ahradnansky/GearIndicator/resources/_HWcomponents/DISP/Q01_ZTTCR8MG.pdf

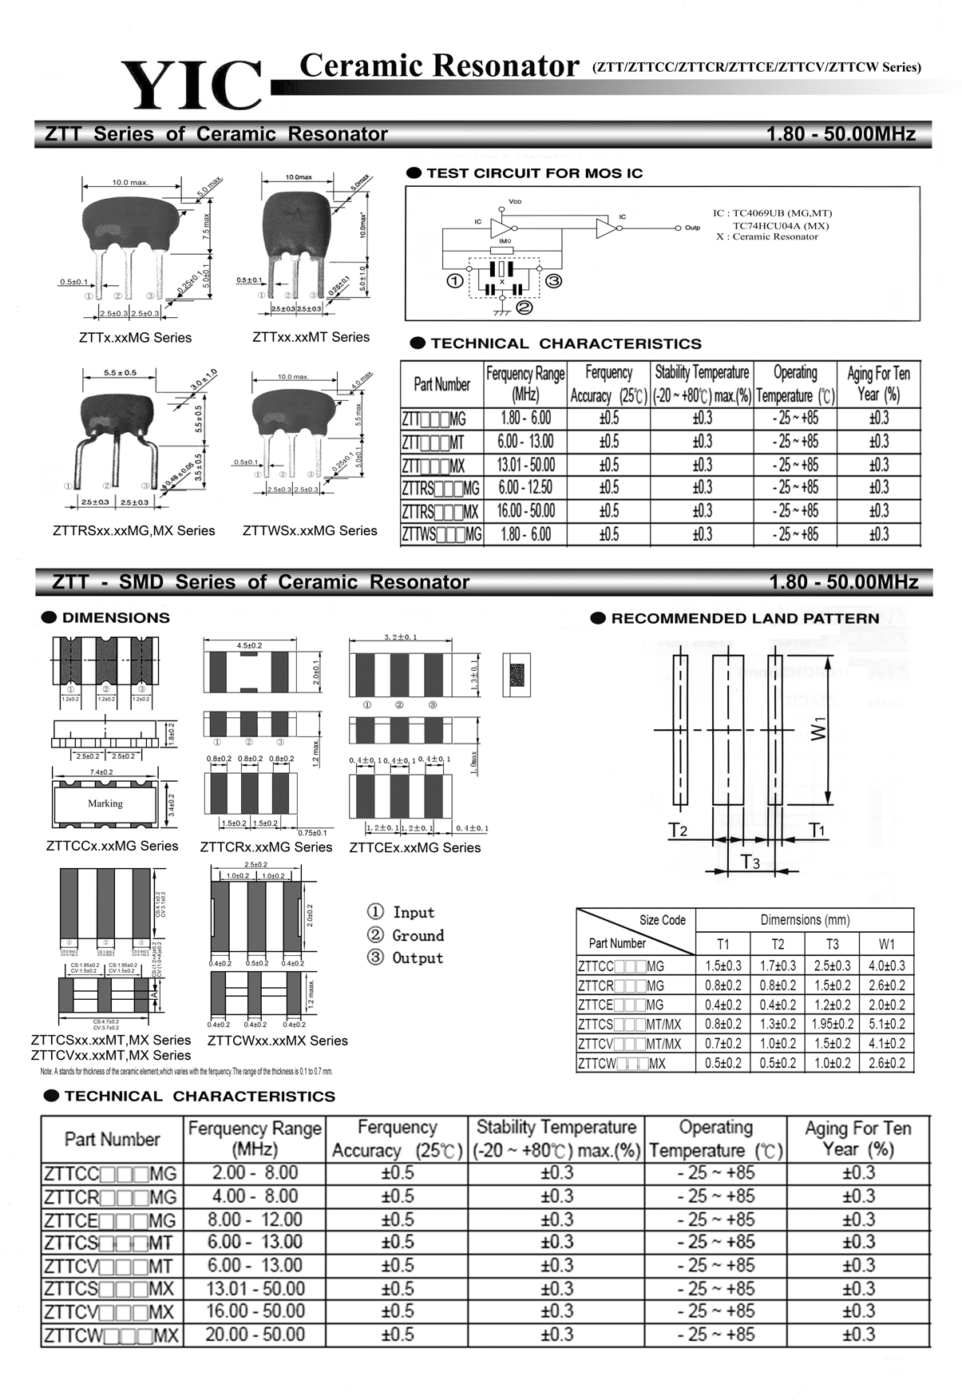
[picture p9: page 1]
