ahradnansky/GearIndicator/resources/_HWcomponents/DISP/R01-11_HP03W5F3300T5E.pdf

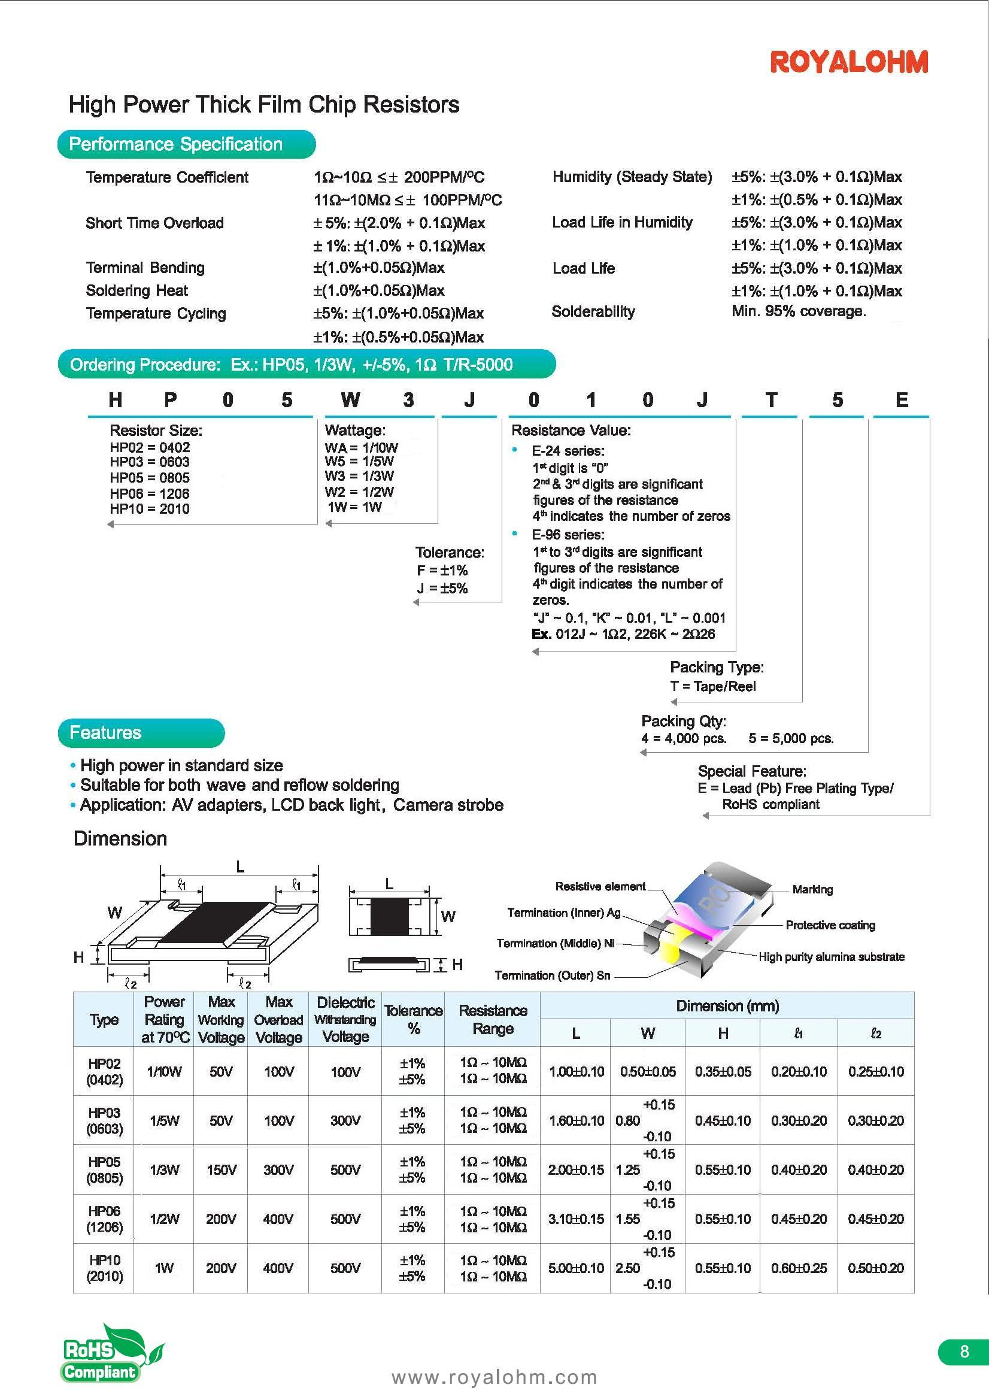
[picture p10: page 1]
