ahradnansky/GearIndicator/resources/_Bikes/HONDA/Honda-data-tables.pdf

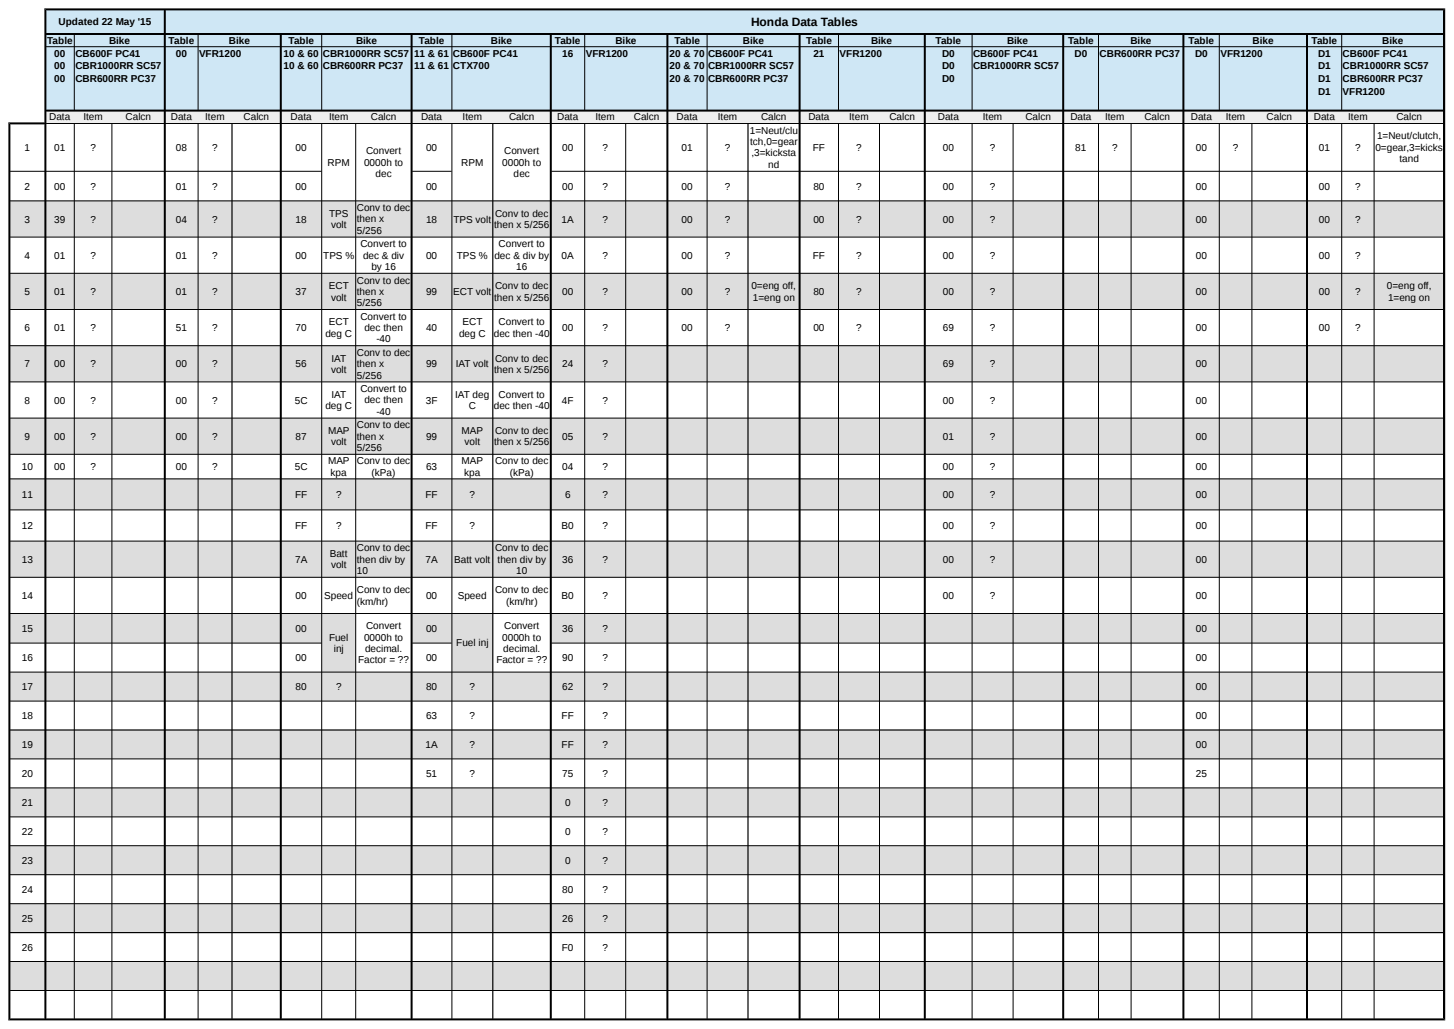
[picture p20: page 1]
Updated 22 May '15; Honda Data Tables; Table; Bike; 00 VFR1200; 10 & 60 CBR1000RR SC57 11 & 61 CB600F PC41; 16 VFR1200; VFR1200; D0 CBR600RR PC37; D0 VFR1200; 00 CBR1000RR SC57; 10 & 60 CBR600RR PC37 11 & 61 CTX700; 20 & 70 CBR1000RR SC57; CBR1000RR SC57; D1 CBR1000RR SC57; 00 CBR600RR PC37; 20 & 70 CBR600RR PC37; D1 CBR600RR PC37; D1 VFR1200; Data Item; Calcn; Data; Item; RPM; TPS volt; TPS %; ECT volt; IAT volt; Batt volt; Speed; Fuel inj; Convert 0000h to dec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

Conv to dec
then x 5/256
Convert to
dec & div by

(kPa)

Batt
then div by
volt
