ahradnansky/GearIndicator/resources/_Bikes/SUZUKI/SDS2OBD.pdf

## OBD to SDS cable wiring diagram

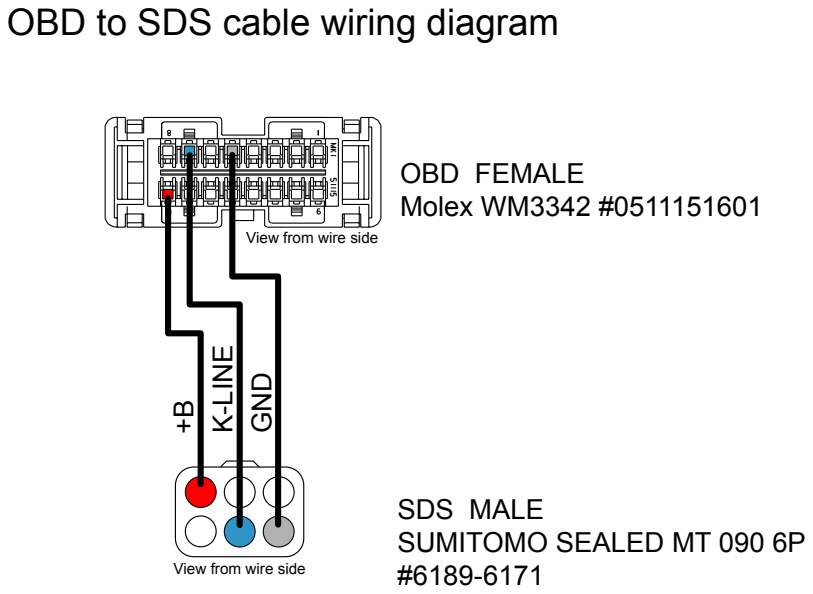
[picture p21: page 1]
OBD FEMALE Molex WM3342 #0511151601; K-LINE; GND

View from wire side

SDS MALE
SUMITOMO SEALED MT 090 6P
